esutlie/blender_creations/blender/stlexports/2021-10-08_16-44-18/stand.stl

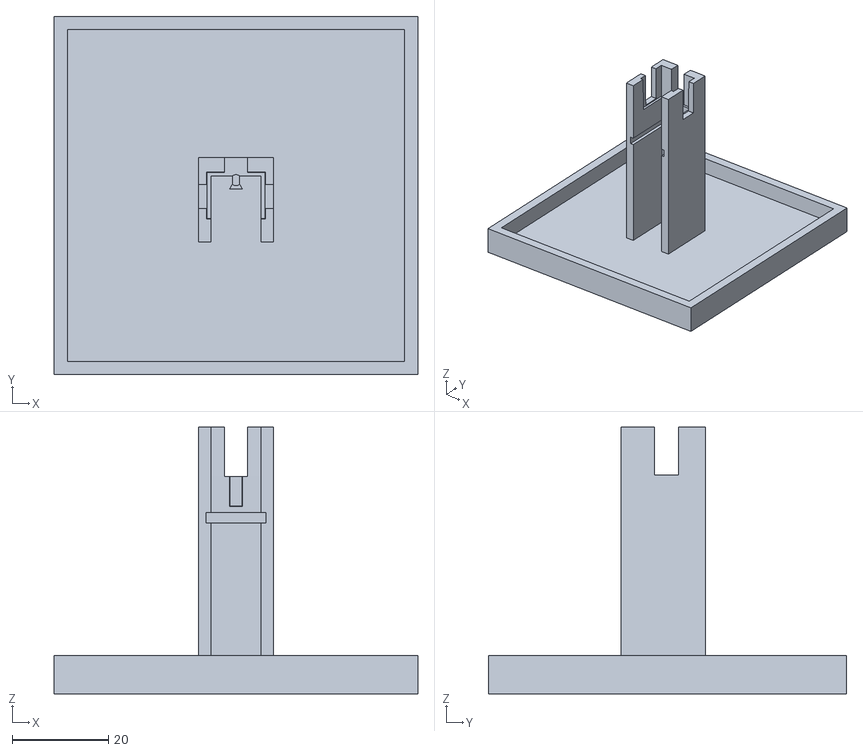
[picture p12: CAD file, 2021-10-22]
blender/stlexports/2021-10-08_16-44-18/stand.stl
75.7 x 74.6 x 55.5
