esutlie/blender_creations/blender/stlexports/2021-10-08_16-51-40/surgery.002.stl

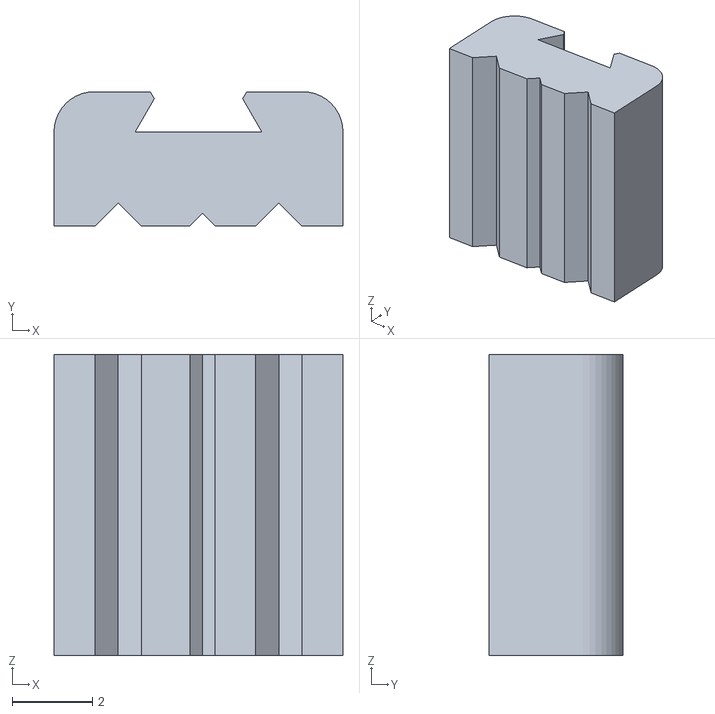
[picture p13: CAD file, 2021-10-22]
blender/stlexports/2021-10-08_16-51-40/surgery.002.stl
7.20 x 3.35 x 7.50
