esutlie/blender_creations/blender/stlexports/2021-10-11_14-52-31/cap0.2,0.13.stl

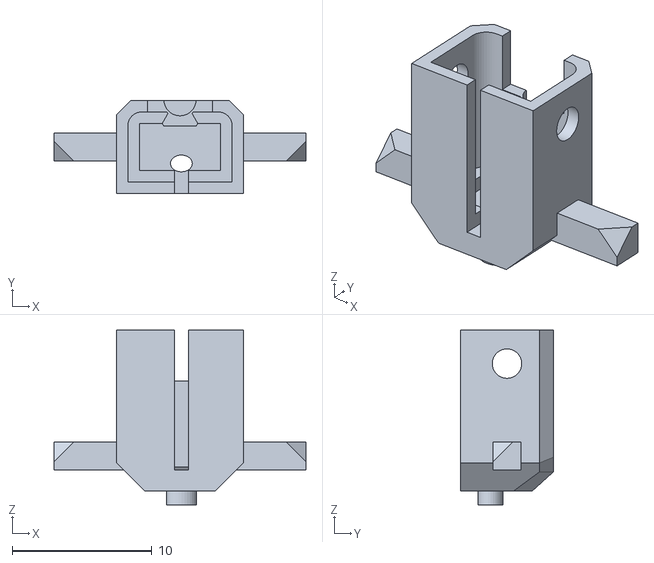
[picture p14: CAD file, 2021-10-22]
blender/stlexports/2021-10-11_14-52-31/cap0.2,0.13.stl
18.0 x 6.61 x 12.5
