esutlie/blender_creations/blender/stlexports/2021-10-11_14-56-39/surgery0.1.stl

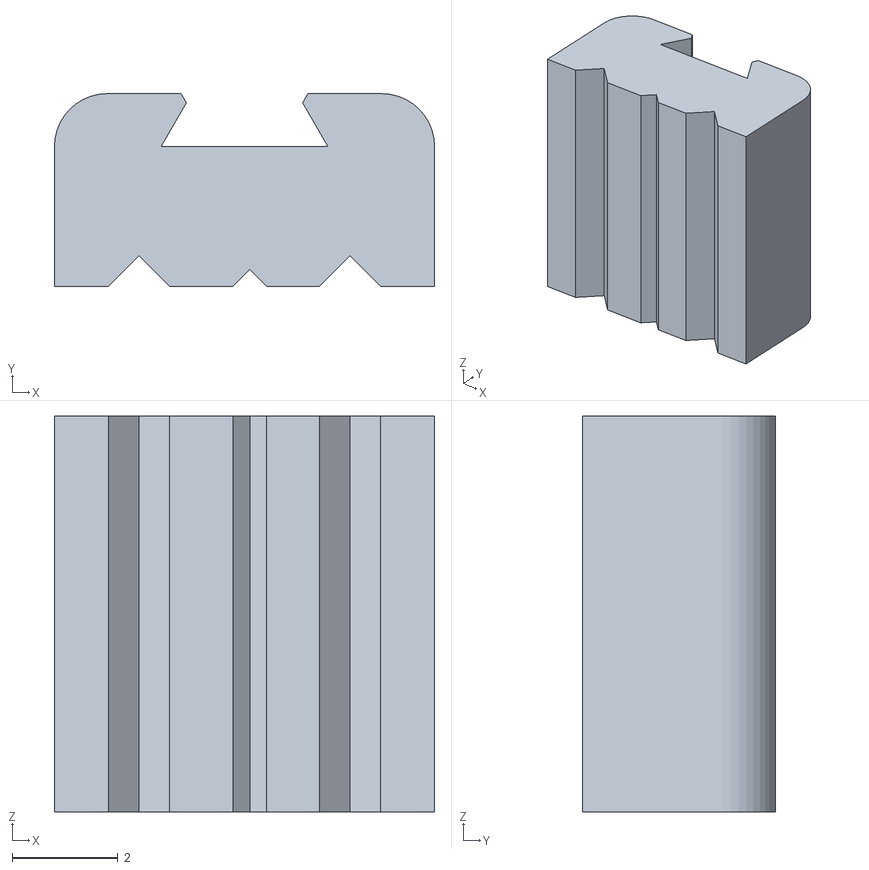
[picture p15: CAD file, 2021-10-22]
blender/stlexports/2021-10-11_14-56-39/surgery0.1.stl
7.20 x 3.65 x 7.50
