esutlie/blender_creations/blender/stlexports/2021-10-12_14-52-41/cover.stl

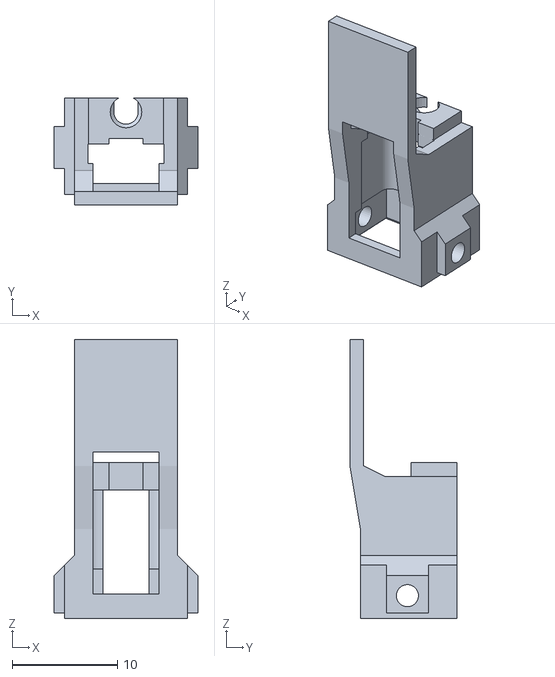
[picture p16: CAD file, 2021-10-22]
blender/stlexports/2021-10-12_14-52-41/cover.stl
13.6 x 10.2 x 26.5
