esutlie/blender_creations/blender/stlexports/2021-10-13_14-44-16/cover0.1.stl

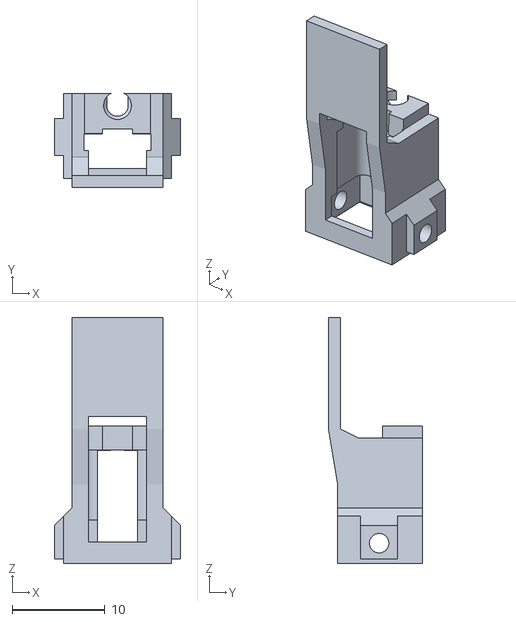
[picture p17: CAD file, 2021-10-22]
blender/stlexports/2021-10-13_14-44-16/cover0.1.stl
13.6 x 10.2 x 26.5
