esutlie/blender_creations/blender/stlexports/2021-10-22_11-58-40/cleaner.stl

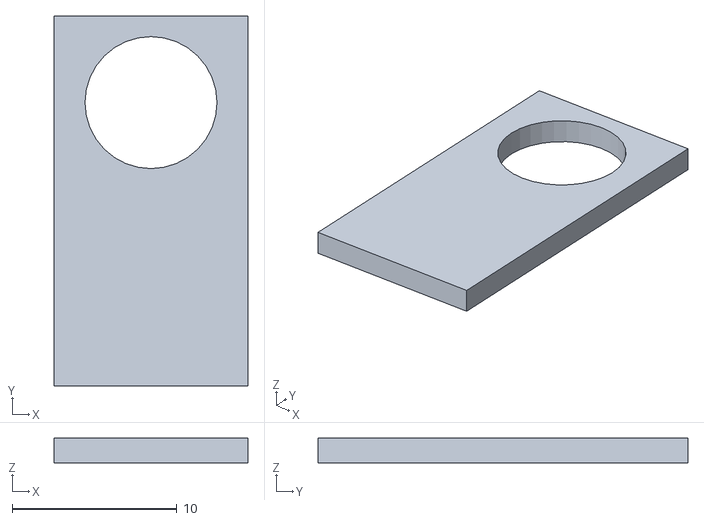
[picture p18: CAD file, 2021-10-29]
blender/stlexports/2021-10-22_11-58-40/cleaner.stl
11.8 x 22.4 x 1.50
