esutlie/blender_creations/blender/stlexports/2021-10-22_17-03-30/holder.stl

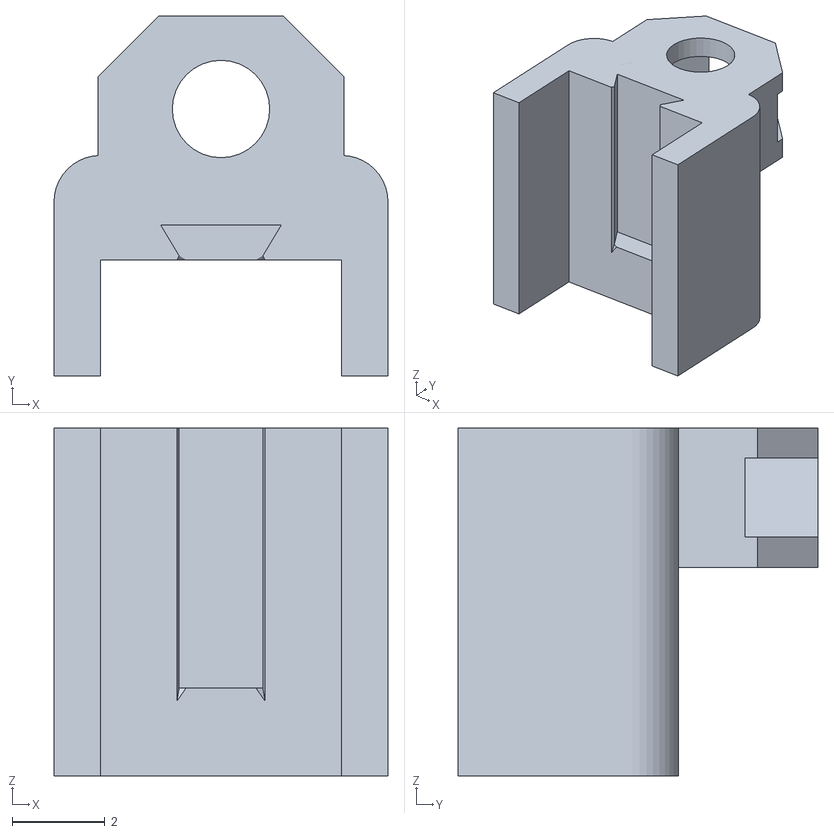
[picture p19: CAD file, 2021-10-29]
blender/stlexports/2021-10-22_17-03-30/holder.stl
7.20 x 7.75 x 7.50
