esutlie/blender_creations/blender/stlexports/2021-10-27_11-30-10/stand_test.stl

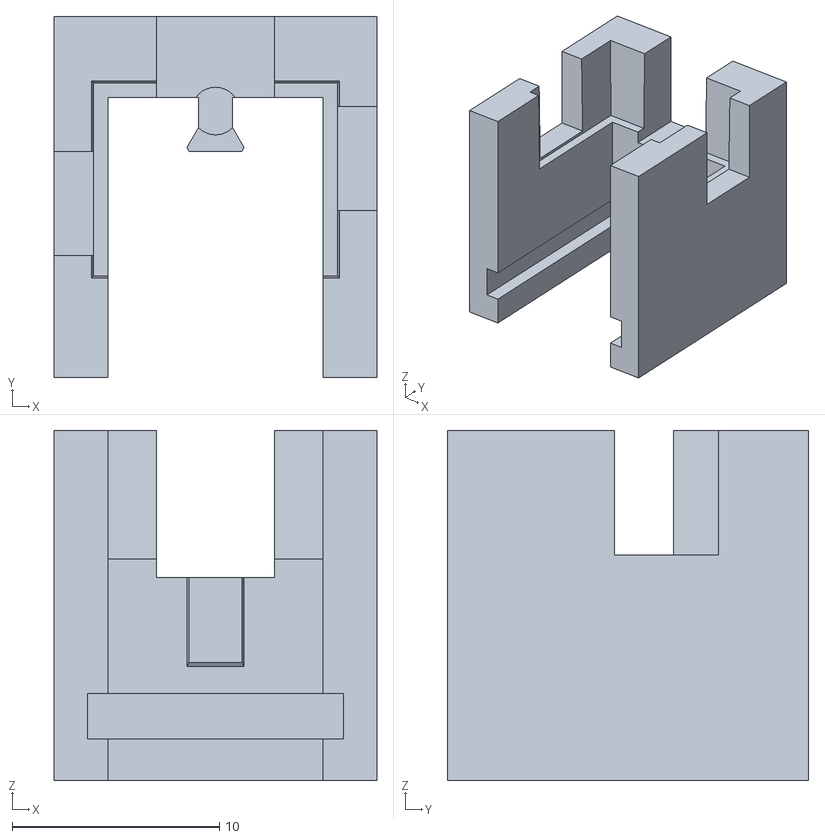
[picture p20: CAD file, 2021-10-29]
blender/stlexports/2021-10-27_11-30-10/stand_test.stl
15.6 x 17.4 x 16.9
