esutlie/blender_creations/blender/stlexports/2021-10-27_16-32-51/cap.stl

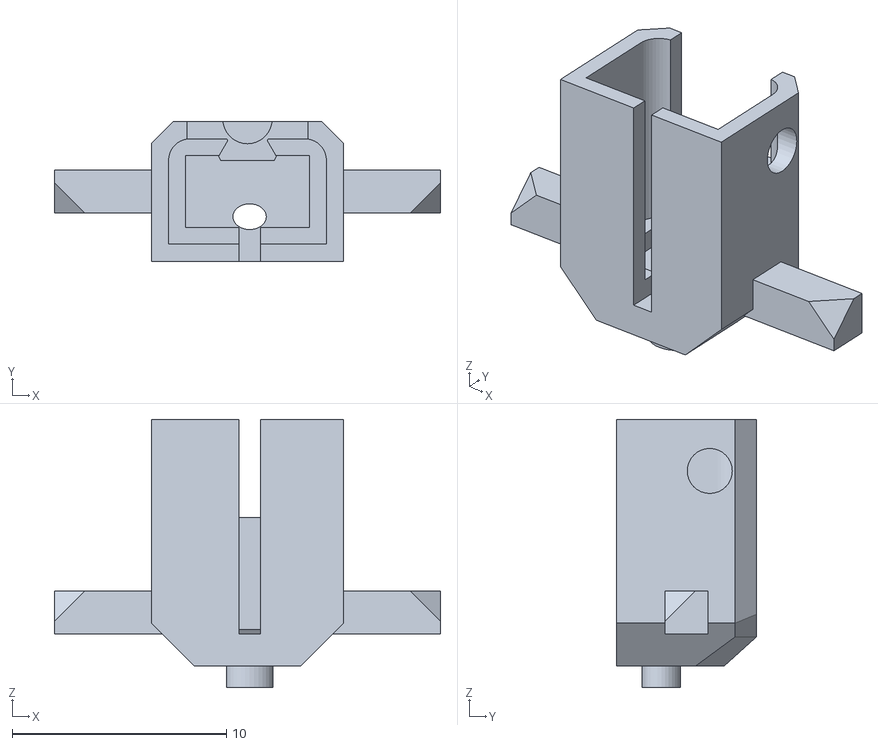
[picture p21: CAD file, 2021-10-29]
blender/stlexports/2021-10-27_16-32-51/cap.stl
18.0 x 6.51 x 12.5
