esutlie/blender_creations/blender/stlexports/2021-10-28_10-04-52/cover.stl

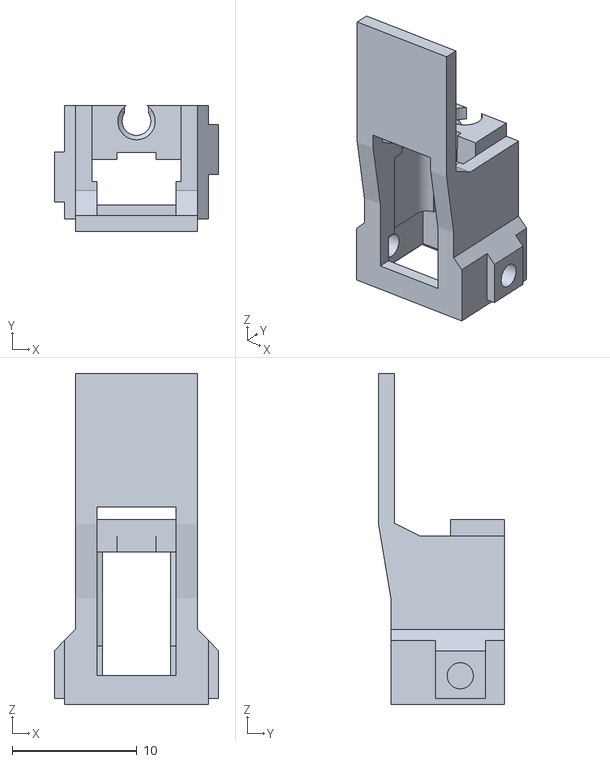
[picture p22: CAD file, 2021-10-29]
blender/stlexports/2021-10-28_10-04-52/cover.stl
13.2 x 10.1 x 26.5
