esutlie/blender_creations/blender/stlexports/2021-11-03_10-34-36/stand_test.stl

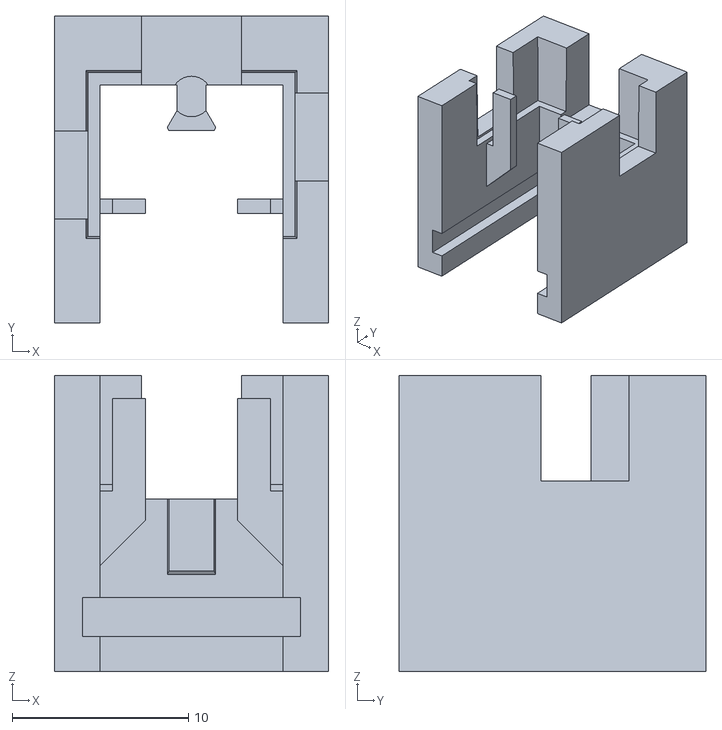
[picture p23: CAD file, 2022-01-04]
blender/stlexports/2021-11-03_10-34-36/stand_test.stl
15.6 x 17.4 x 16.8
