esutlie/blender_creations/blender/stlexports/2021-11-15_14-42-10/cam_cover.stl

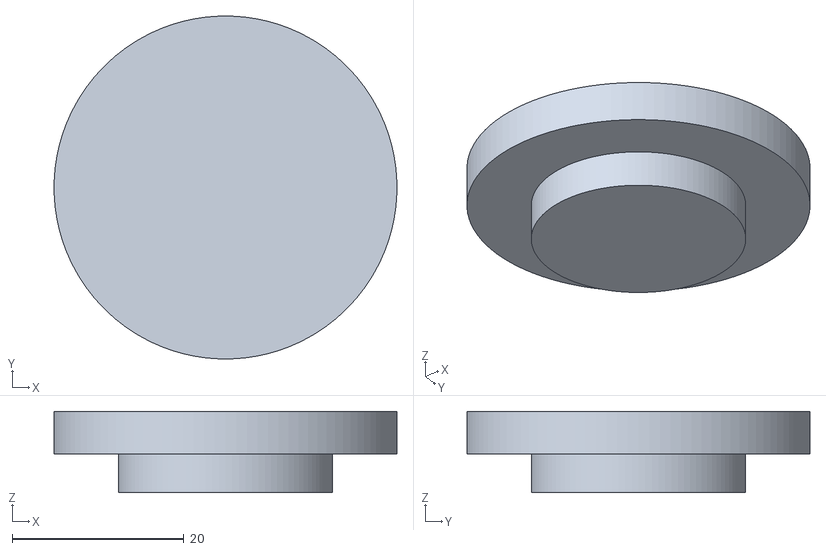
[picture p24: CAD file, 2022-01-04]
blender/stlexports/2021-11-15_14-42-10/cam_cover.stl
40.0 x 40.0 x 9.50
