esutlie/blender_creations/blender/stlexports/2021-11-15_14-51-04/stand.stl

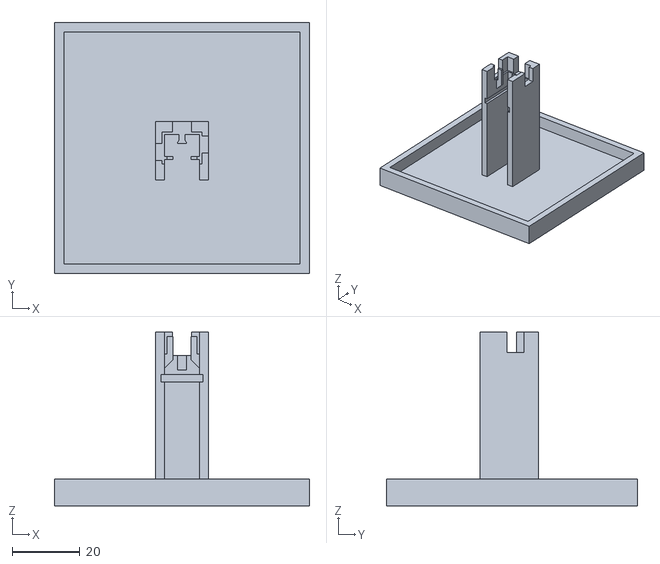
[picture p25: CAD file, 2022-01-04]
blender/stlexports/2021-11-15_14-51-04/stand.stl
75.6 x 74.4 x 51.5
