esutlie/blender_creations/blender/stlexports/2021-11-29_10-13-55/cam_attach.stl

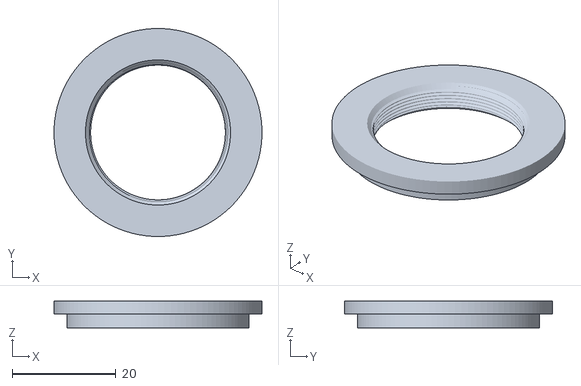
[picture p26: CAD file, 2022-01-04]
blender/stlexports/2021-11-29_10-13-55/cam_attach.stl
40.0 x 40.0 x 5.10
