esutlie/blender_creations/blender/stlexports/2021-12-08_10-14-58/holder.stl

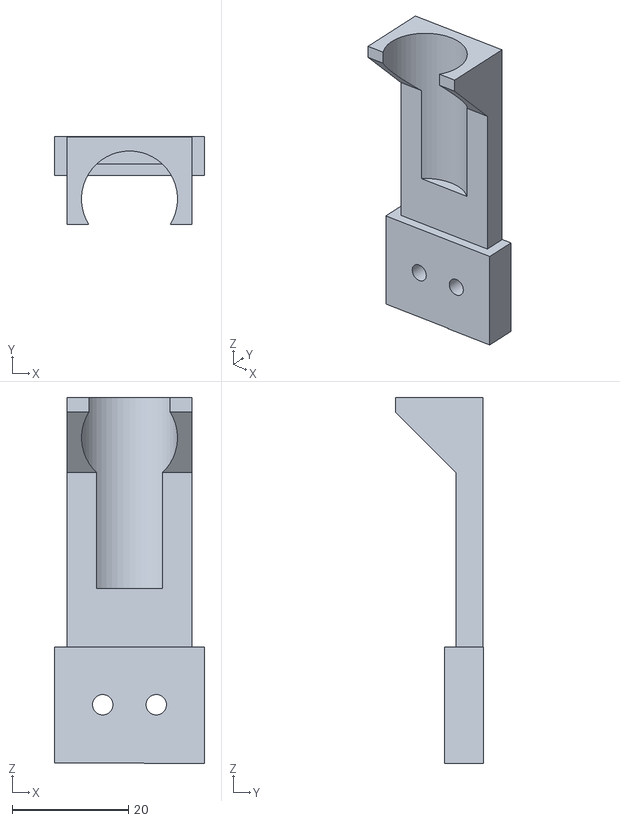
[picture p27: CAD file, 2022-01-04]
blender/stlexports/2021-12-08_10-14-58/holder.stl
25.8 x 15.1 x 62.9
