esutlie/blender_creations/blender/stlexports/2021-12-08_15-39-04/holder.stl

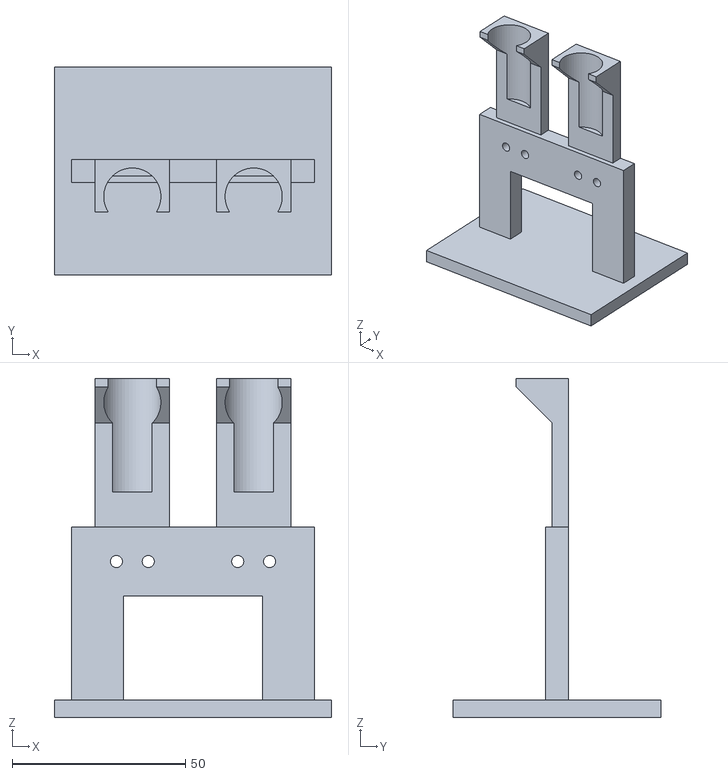
[picture p28: CAD file, 2022-01-04]
blender/stlexports/2021-12-08_15-39-04/holder.stl
80.0 x 60.0 x 97.8
