esutlie/blender_creations/blender/stlexports/2021-12-09_09-44-28/holder.stl

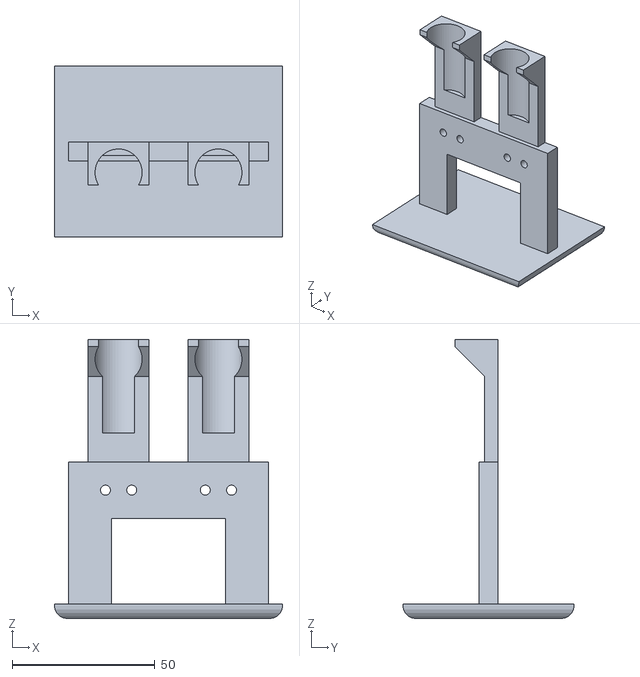
[picture p29: CAD file, 2022-01-04]
blender/stlexports/2021-12-09_09-44-28/holder.stl
80.0 x 60.0 x 97.8
