esutlie/blender_creations/blender/stlexports/2021-12-09_09-47-33/holder.stl

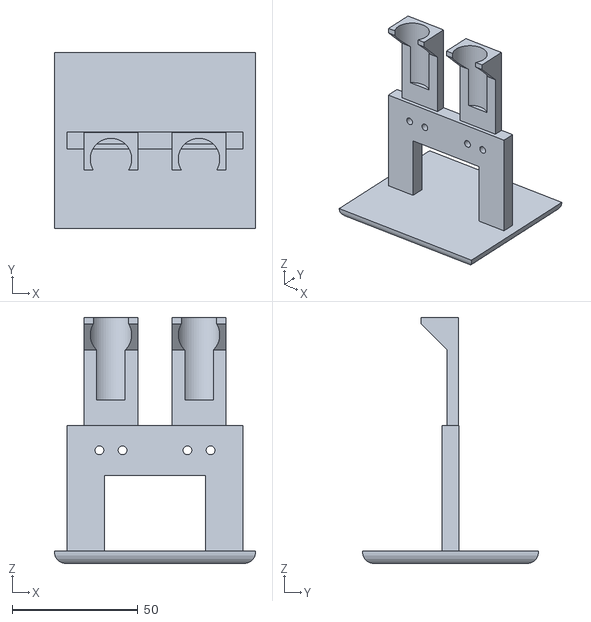
[picture p30: CAD file, 2022-01-04]
blender/stlexports/2021-12-09_09-47-33/holder.stl
80.0 x 70.0 x 97.8
