esutlie/blender_creations/blender/stlexports/2021-12-14_14-30-24/tri.stl

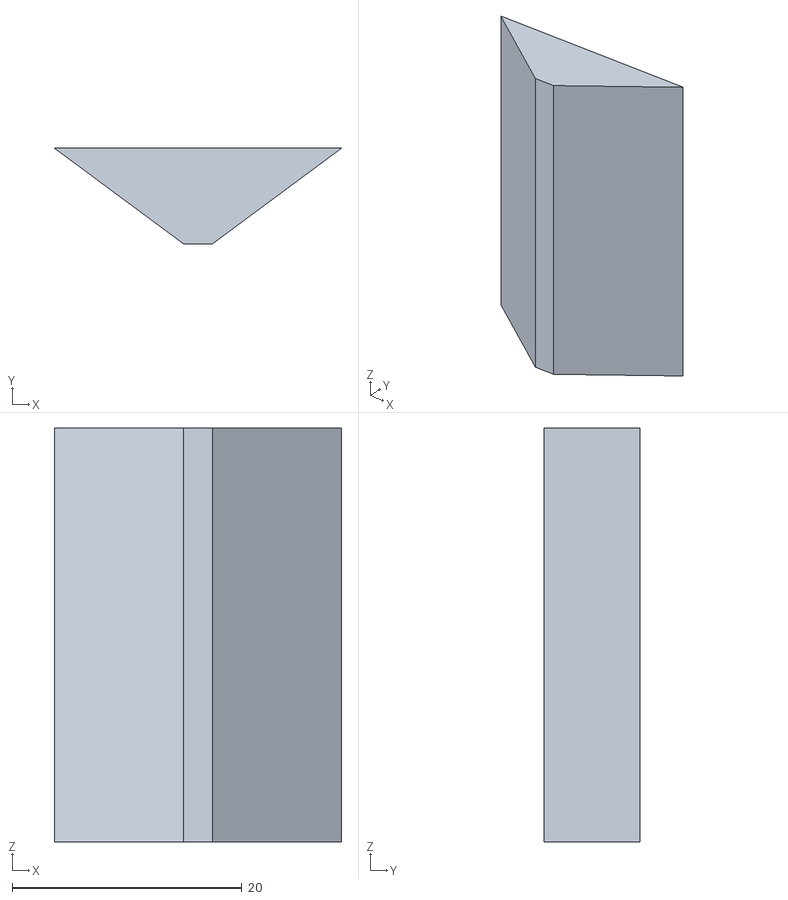
[picture p31: CAD file, 2022-01-04]
blender/stlexports/2021-12-14_14-30-24/tri.stl
25.0 x 8.33 x 36.0
