esutlie/blender_creations/blender/stlexports/2021-12-14_15-07-16/tri.stl

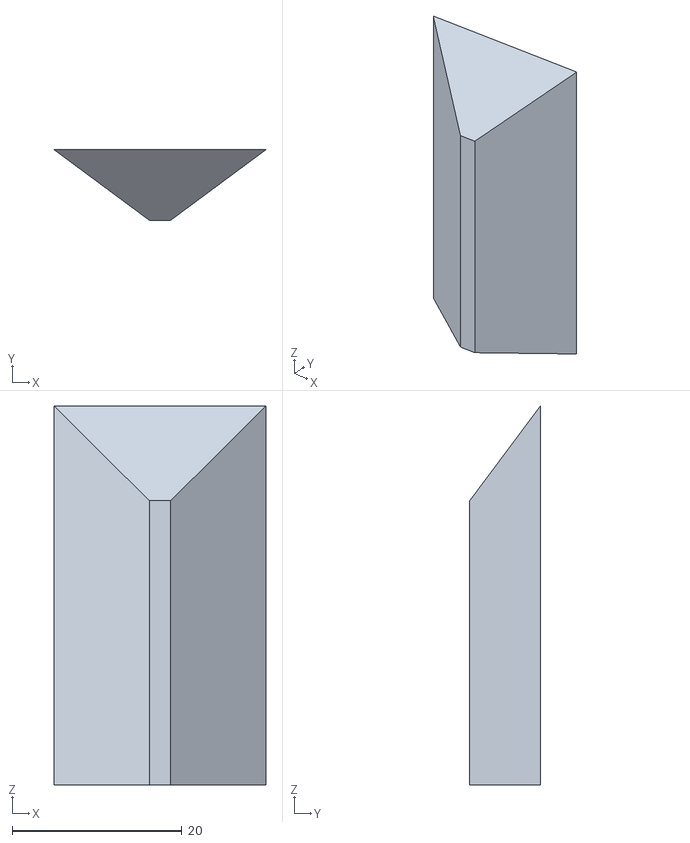
[picture p32: CAD file, 2022-01-04]
blender/stlexports/2021-12-14_15-07-16/tri.stl
25.0 x 8.33 x 44.7
