esutlie/blender_creations/blender/stlexports/2021-12-15_12-07-13/backer.stl

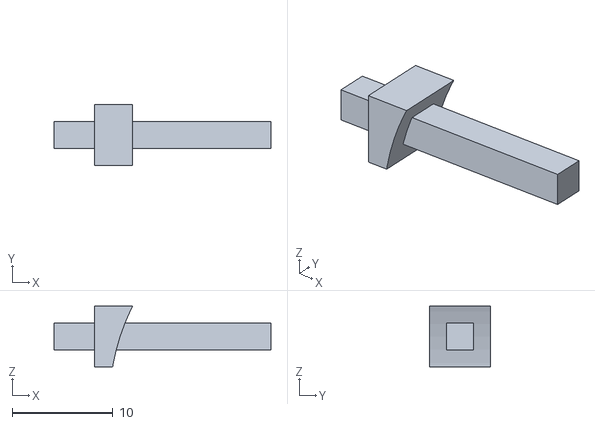
[picture p33: CAD file, 2022-01-04]
blender/stlexports/2021-12-15_12-07-13/backer.stl
21.5 x 6.00 x 6.00
