esutlie/blender_creations/blender/stlexports/2022-01-04_11-12-24/tube.stl

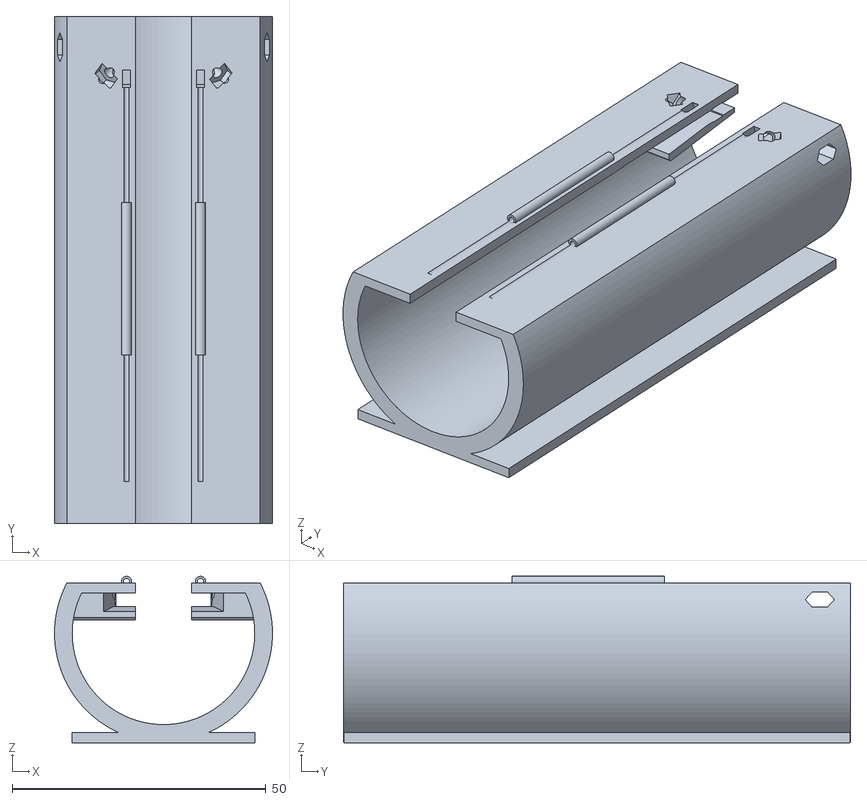
[picture p34: CAD file, 2022-01-04]
blender/stlexports/2022-01-04_11-12-24/tube.stl
43.0 x 100.0 x 32.9
