esutlie/blender_creations/blender/stlexports/2022-01-05_09-46-58/holder.stl

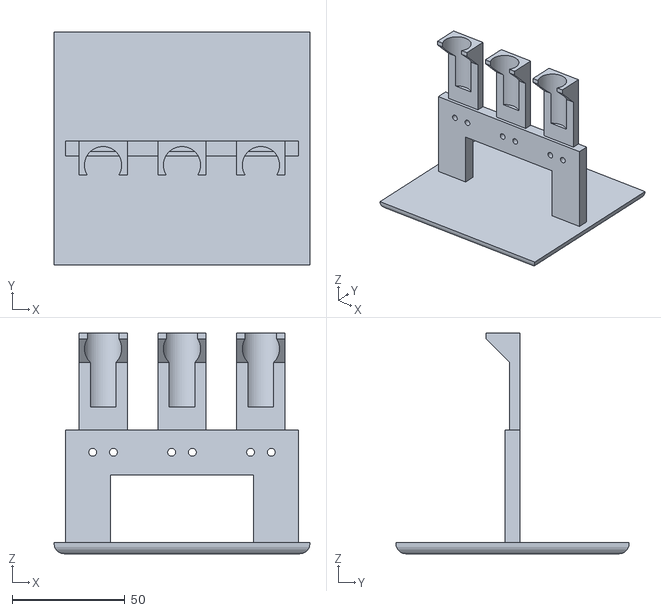
[picture p35: CAD file, 2022-01-31]
blender/stlexports/2022-01-05_09-46-58/holder.stl
113.5 x 103.5 x 97.8
