esutlie/blender_creations/blender/stlexports/2022-01-05_09-47-00/creation.stl

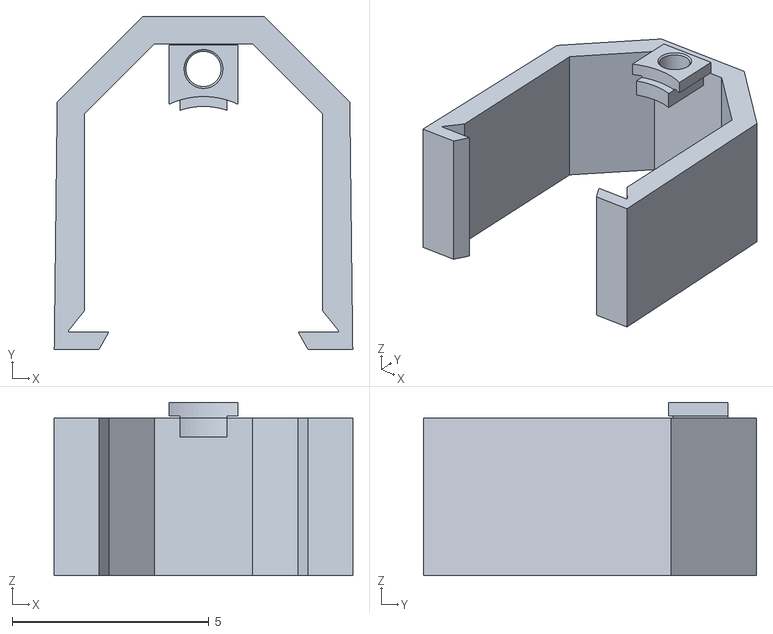
[picture p36: CAD file, 2022-01-31]
blender/stlexports/2022-01-05_09-47-00/creation.stl
7.58 x 8.46 x 4.40
