esutlie/blender_creations/blender/stlexports/2022-01-28_13-01-05/cable_cover.stl

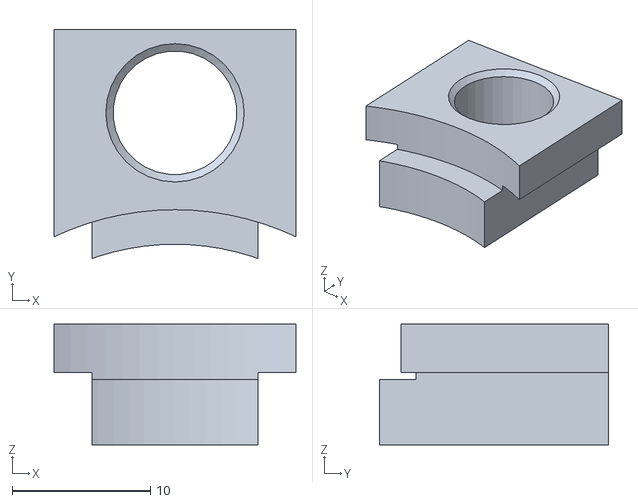
[picture p37: CAD file, 2022-01-31]
blender/stlexports/2022-01-28_13-01-05/cable_cover.stl
17.5 x 16.6 x 8.75
