esutlie/blender_creations/blender/stlexports/2022-02-18_14-35-42/cleaner.stl

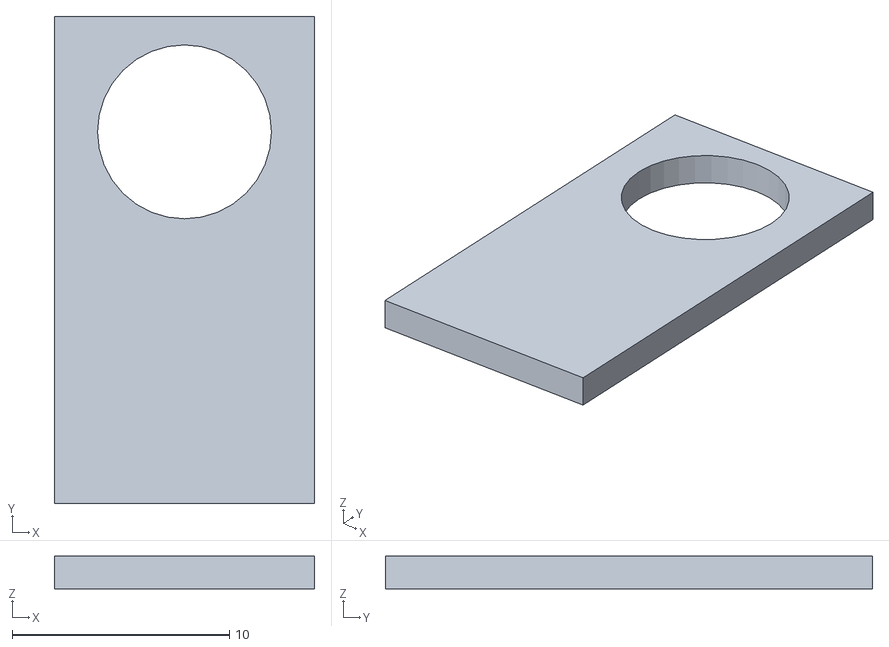
[picture p38: CAD file, 2022-02-21]
blender/stlexports/2022-02-18_14-35-42/cleaner.stl
12.0 x 22.4 x 1.50
