esutlie/blender_creations/blender/stlexports/2022-02-25_14-08-06/cover.stl

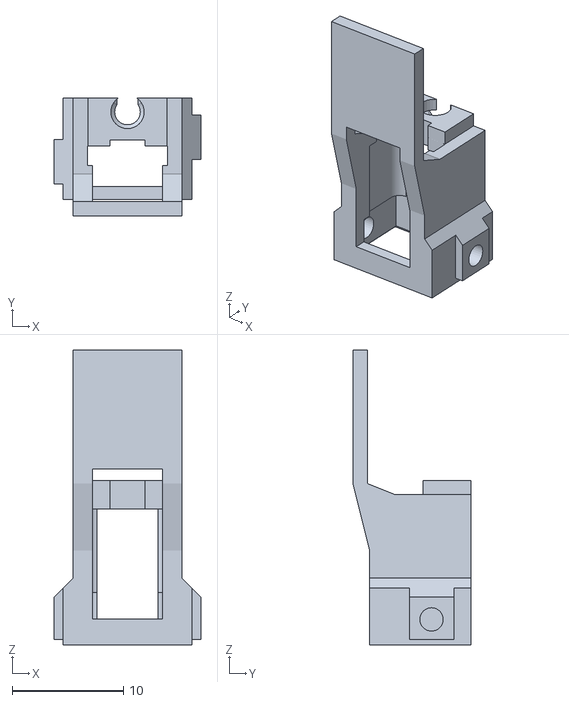
[picture p39: CAD file, 2022-09-09]
blender/stlexports/2022-02-25_14-08-06/cover.stl
13.2 x 10.6 x 26.5
