esutlie/blender_creations/blender/stlexports/2022-03-31_11-08-54/port.stl

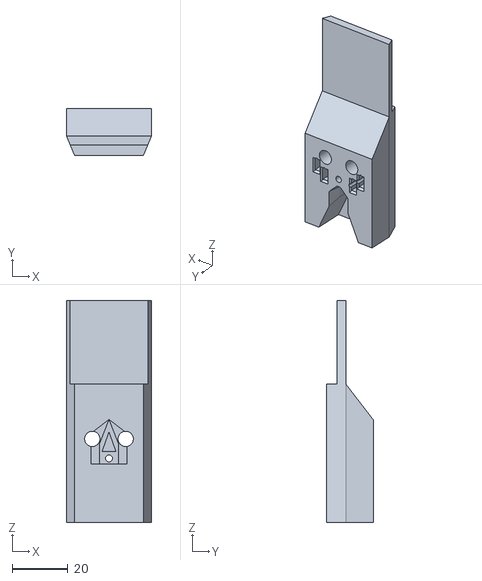
[picture p40: CAD file, 2022-09-09]
blender/stlexports/2022-03-31_11-08-54/port.stl
30.5 x 17.0 x 79.7
