esutlie/blender_creations/blender/stlexports/2022-04-05_10-54-50/port.stl

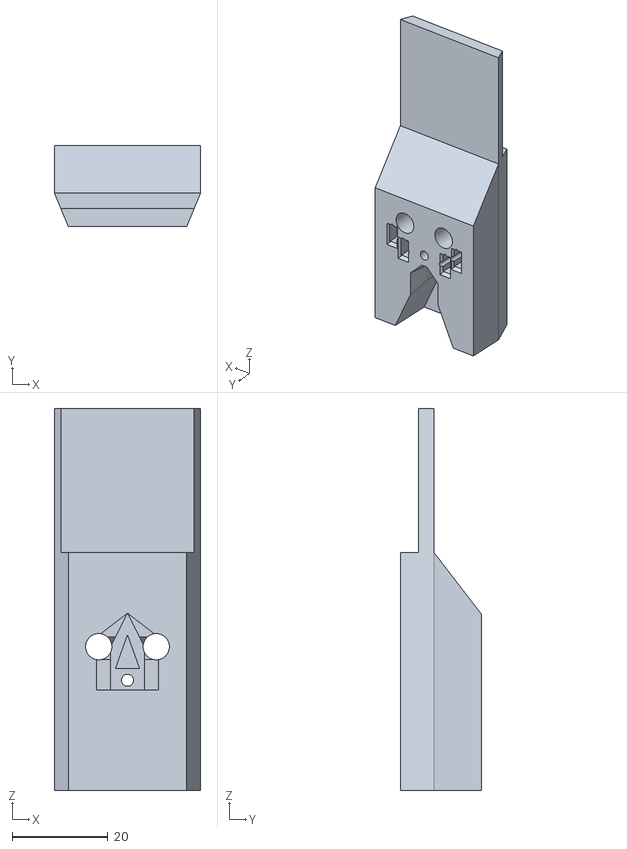
[picture p41: CAD file, 2022-09-09]
blender/stlexports/2022-04-05_10-54-50/port.stl
30.5 x 17.0 x 79.7
