esutlie/blender_creations/blender/stlexports/2022-05-19_14-07-43_tictac/frame.stl

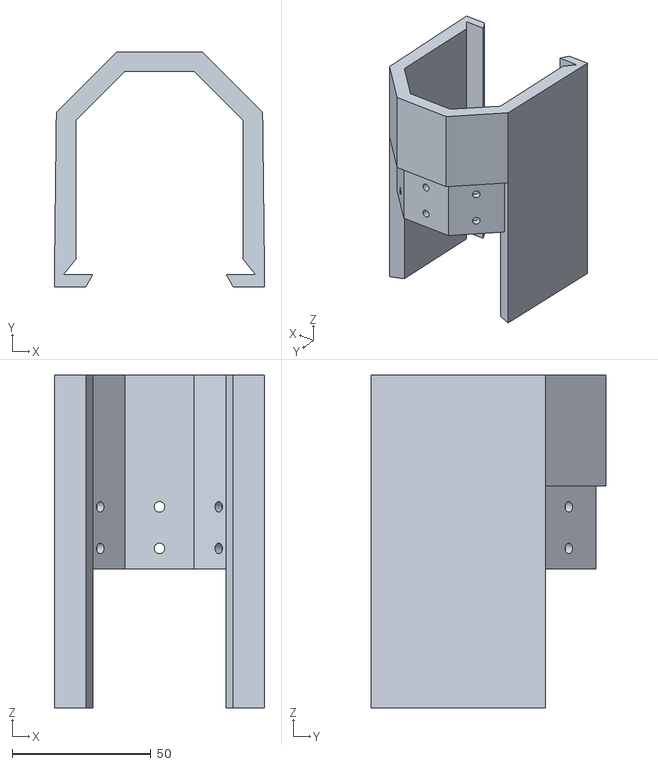
[picture p42: CAD file, 2022-09-09]
blender/stlexports/2022-05-19_14-07-43_tictac/frame.stl
75.8 x 84.6 x 120.0
