esutlie/blender_creations/blender/stlexports/2022-08-19_12-06-19/cap0.02.stl

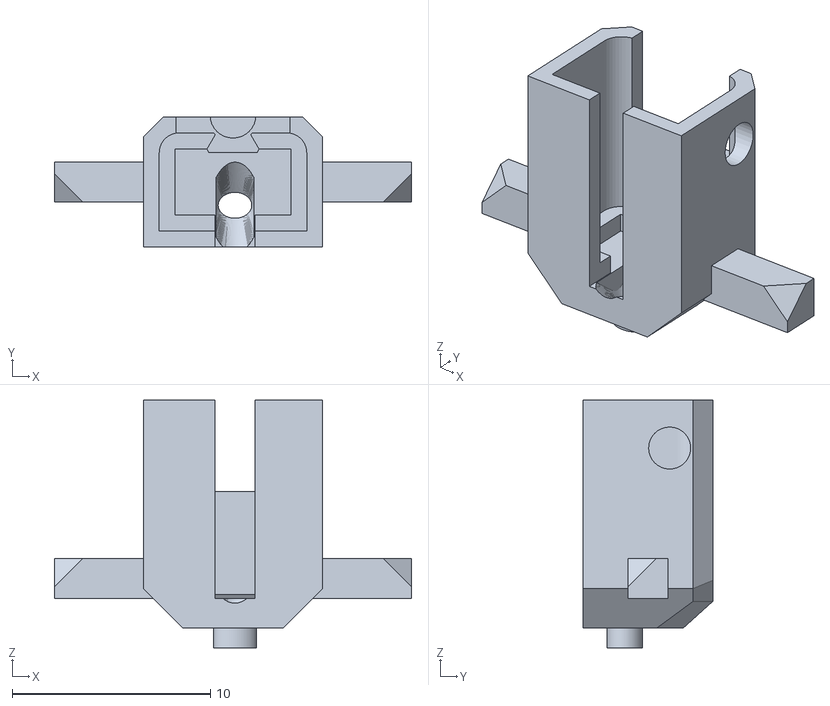
[picture p43: CAD file, 2022-09-09]
blender/stlexports/2022-08-19_12-06-19/cap0.02.stl
18.0 x 6.55 x 12.5
