esutlie/blender_creations/blender/stlexports/2022-08-19_12-06-27/cover0.04.stl

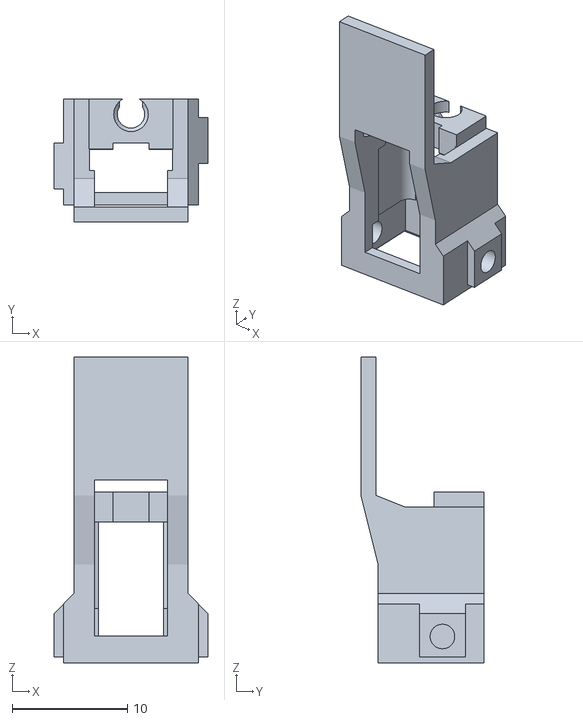
[picture p44: CAD file, 2022-09-09]
blender/stlexports/2022-08-19_12-06-27/cover0.04.stl
13.3 x 10.7 x 26.5
