esutlie/blender_creations/blender/stlexports/2022-08-19_12-06-36/surgery0.06.stl

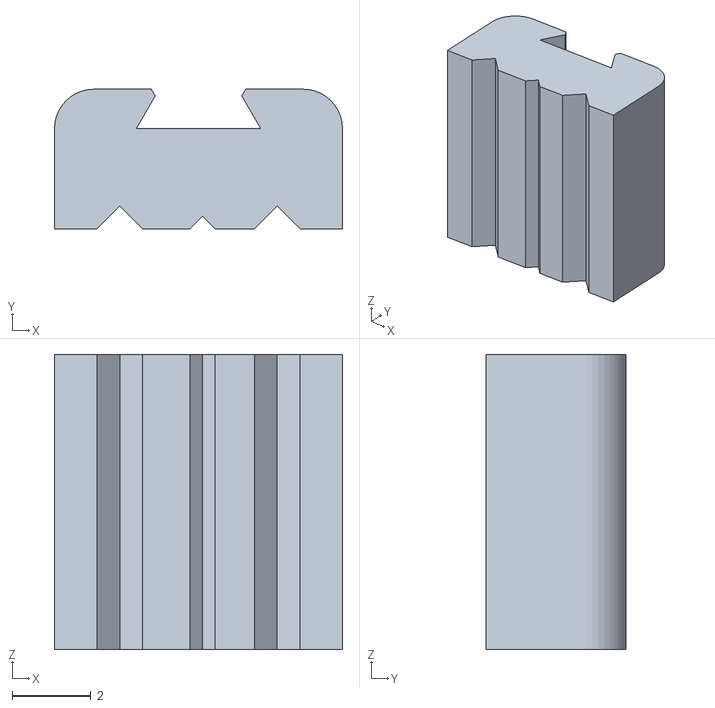
[picture p45: CAD file, 2022-09-09]
blender/stlexports/2022-08-19_12-06-36/surgery0.06.stl
7.32 x 3.55 x 7.50
