esutlie/blender_creations/blender/stlexports/2022-08-19_12-06-45/cap0.08.stl

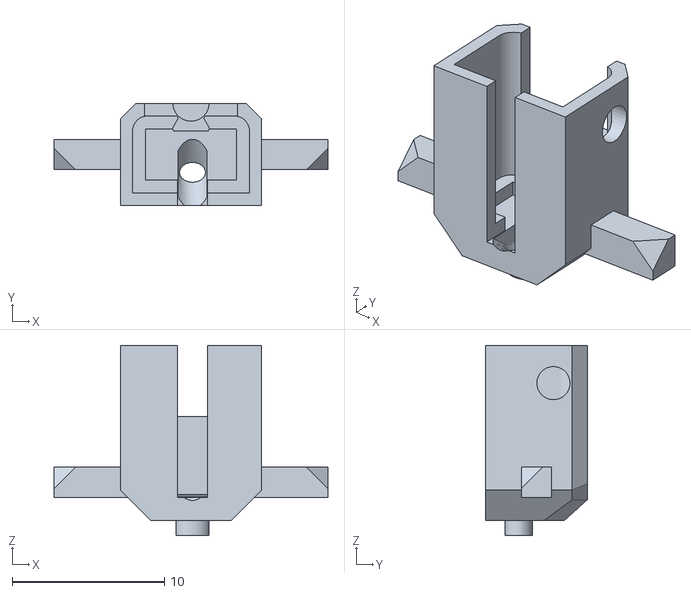
[picture p46: CAD file, 2022-09-09]
blender/stlexports/2022-08-19_12-06-45/cap0.08.stl
18.0 x 6.67 x 12.5
