esutlie/blender_creations/blender/stlexports/2022-08-19_12-06-52/holder0.1.stl

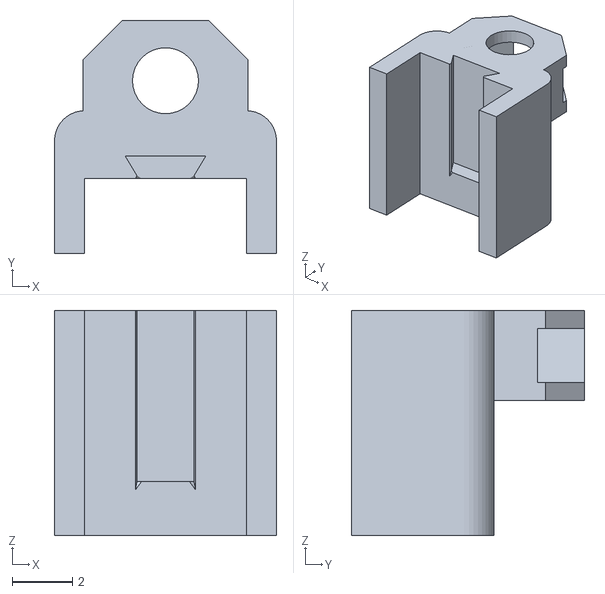
[picture p47: CAD file, 2022-09-09]
blender/stlexports/2022-08-19_12-06-52/holder0.1.stl
7.40 x 7.75 x 7.50
