esutlie/blender_creations/blender/stlexports/2022-08-22_11-59-44/cap-0.06.stl

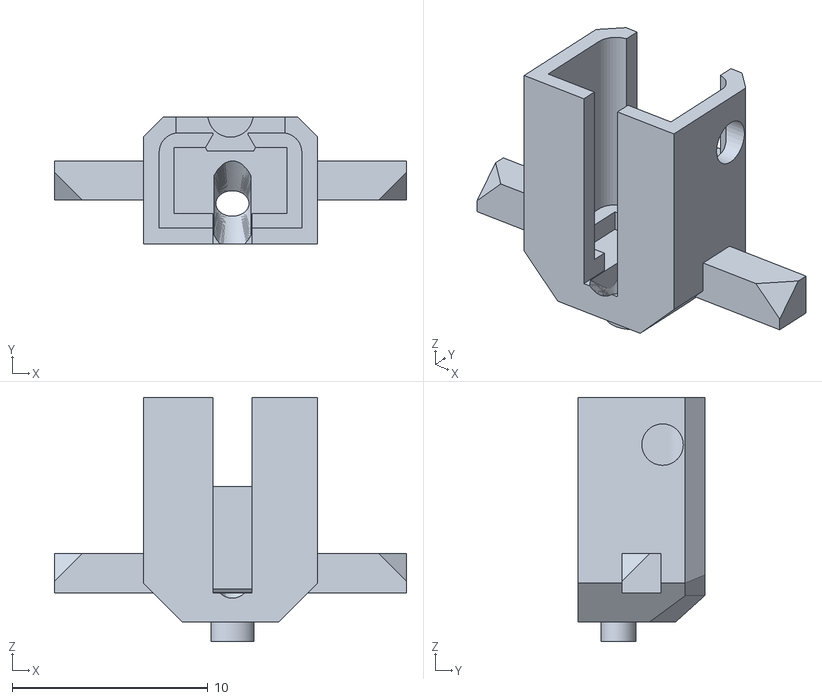
[picture p48: CAD file, 2022-09-09]
blender/stlexports/2022-08-22_11-59-44/cap-0.06.stl
18.0 x 6.47 x 12.5
