esutlie/blender_creations/blender/stlexports/2022-08-22_11-59-57/stopper0.06.stl

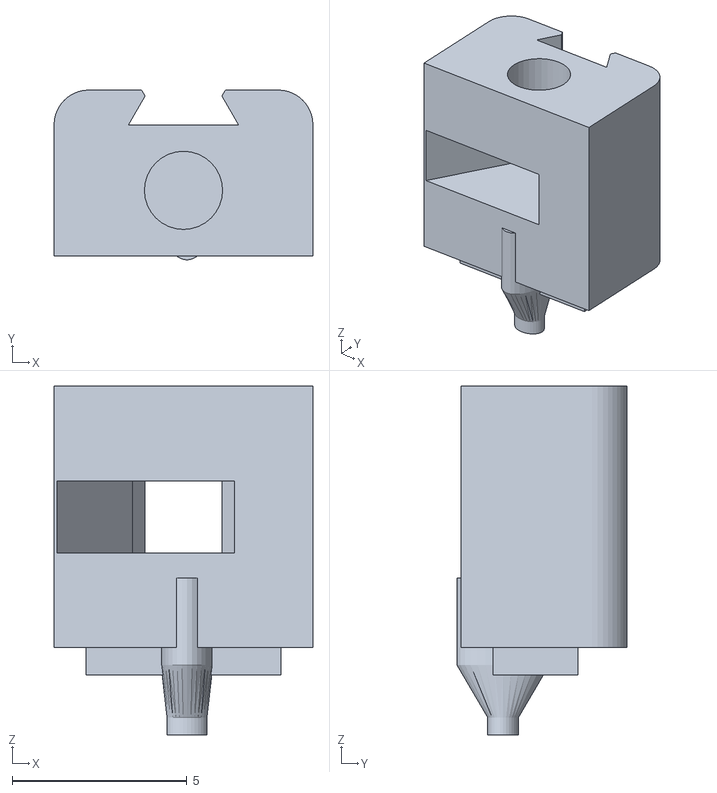
[picture p49: CAD file, 2022-09-09]
blender/stlexports/2022-08-22_11-59-57/stopper0.06.stl
7.42 x 4.87 x 10.0
