esutlie/blender_creations/blender/stlexports/2022-08-22_17-14-23/holder0.001.stl

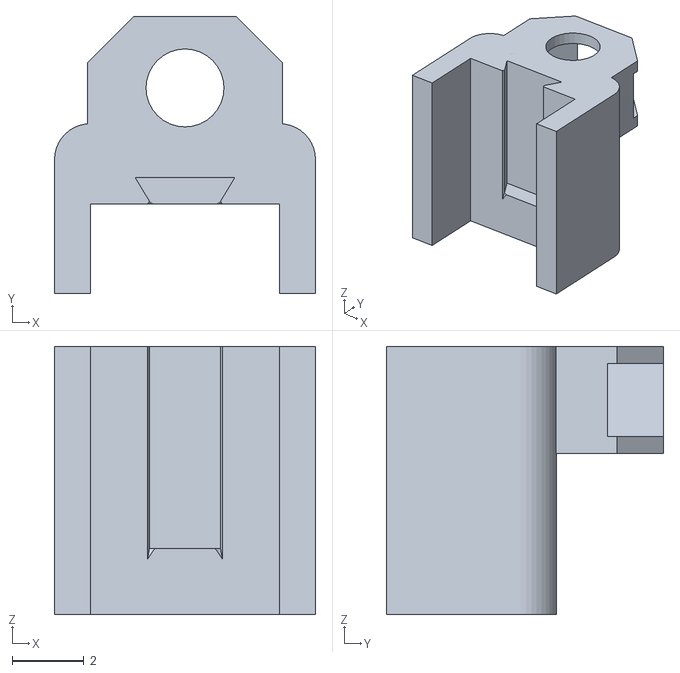
[picture p50: CAD file, 2022-09-09]
blender/stlexports/2022-08-22_17-14-23/holder0.001.stl
7.30 x 7.75 x 7.50
