esutlie/blender_creations/blender/stlexports/2022-08-22_17-14-26/cap0.stl

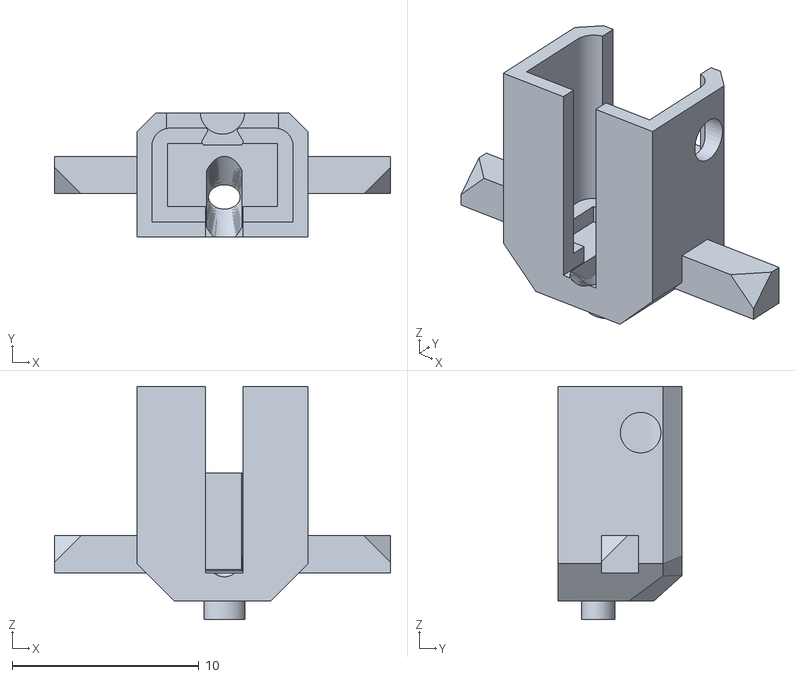
[picture p51: CAD file, 2022-09-09]
blender/stlexports/2022-08-22_17-14-26/cap0.stl
18.0 x 6.63 x 12.5
