esutlie/blender_creations/blender/stlexports/2022-08-23_11-19-07/stand.stl

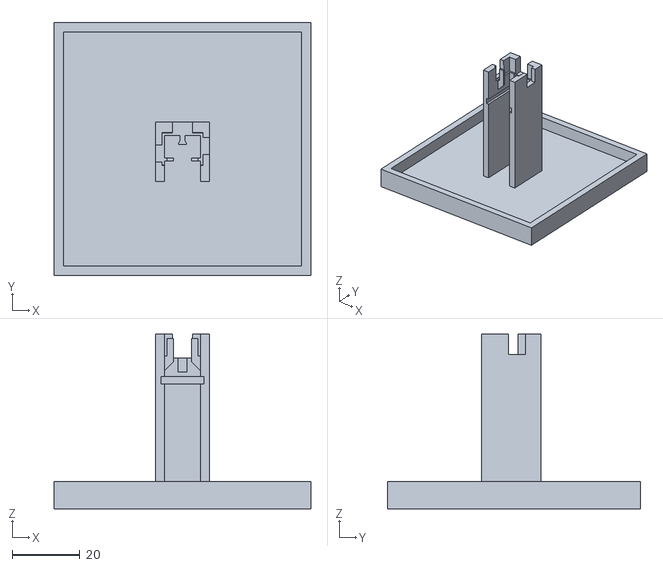
[picture p52: CAD file, 2022-09-09]
blender/stlexports/2022-08-23_11-19-07/stand.stl
75.8 x 74.6 x 51.5
