esutlie/blender_creations/blender/stlexports/2022-08-23_16-00-06/cap0.stl

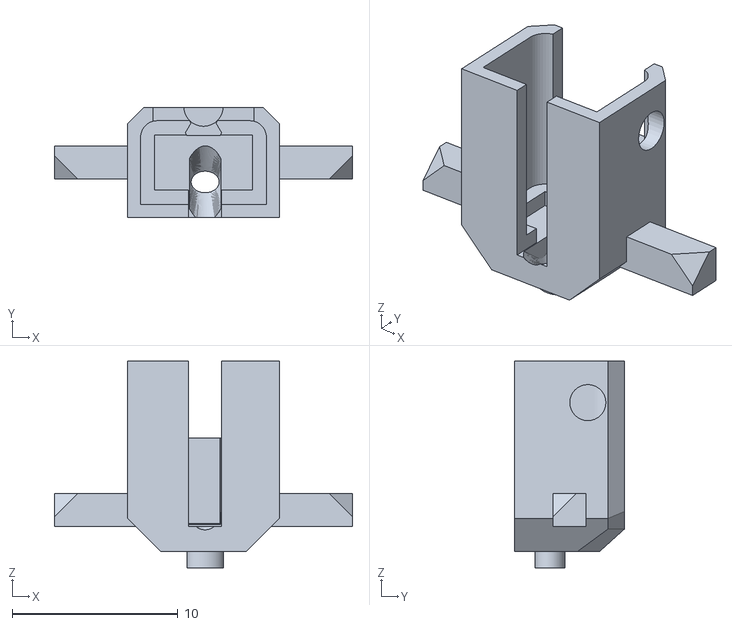
[picture p53: CAD file, 2022-09-09]
blender/stlexports/2022-08-23_16-00-06/cap0.stl
18.0 x 6.65 x 12.5
