esutlie/blender_creations/blender/stlexports/2022-08-30_17-17-07/holder0.6.stl

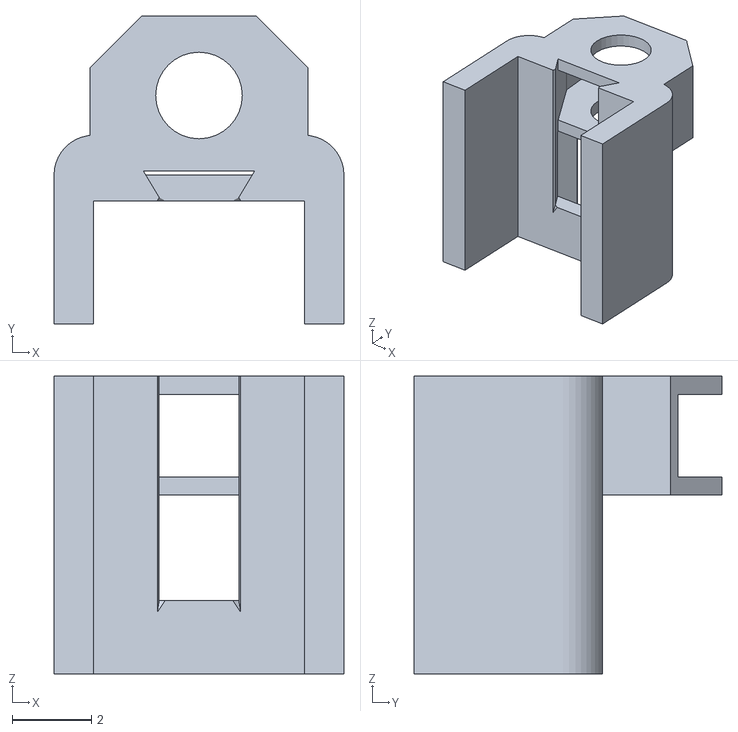
[picture p55: CAD file, 2022-09-09]
blender/stlexports/2022-08-30_17-17-07/holder0.6.stl
7.30 x 7.75 x 7.50
