esutlie/blender_creations/blender/stlexports/2021-09-28_10-52-53/holder.stl

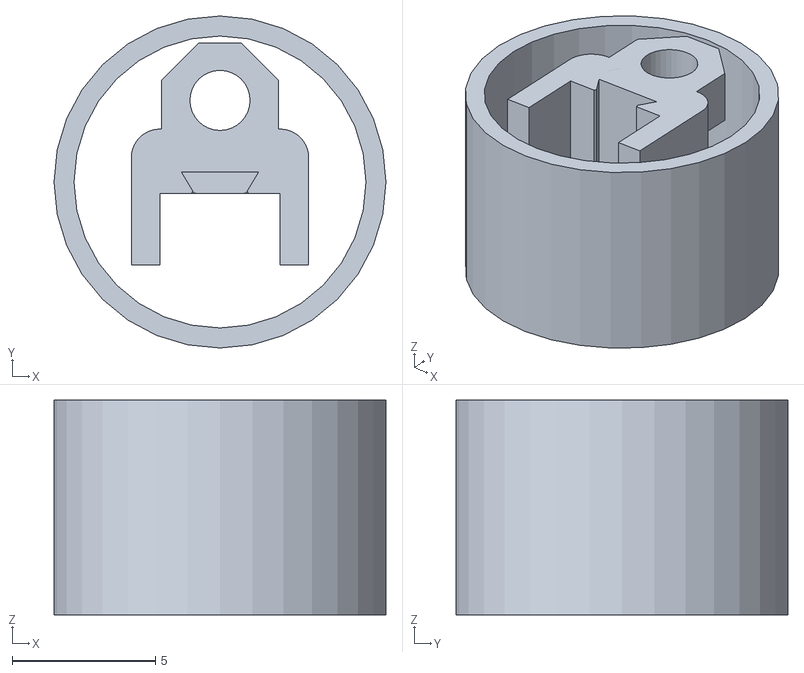
[picture p56: CAD file, 2021-10-06]
blender/stlexports/2021-09-28_10-52-53/holder.stl
11.6 x 11.6 x 7.50
