esutlie/blender_creations/blender/stlexports/2021-09-29_13-45-59/cap.stl

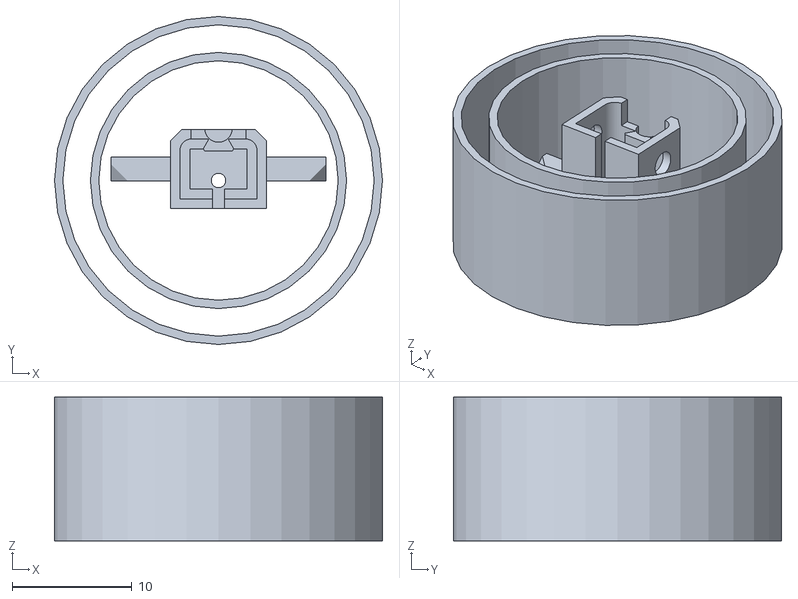
[picture p57: CAD file, 2021-10-06]
blender/stlexports/2021-09-29_13-45-59/cap.stl
27.4 x 27.4 x 12.0
