esutlie/blender_creations/blender/stlexports/2021-10-07_14-18-41/stopper.stl

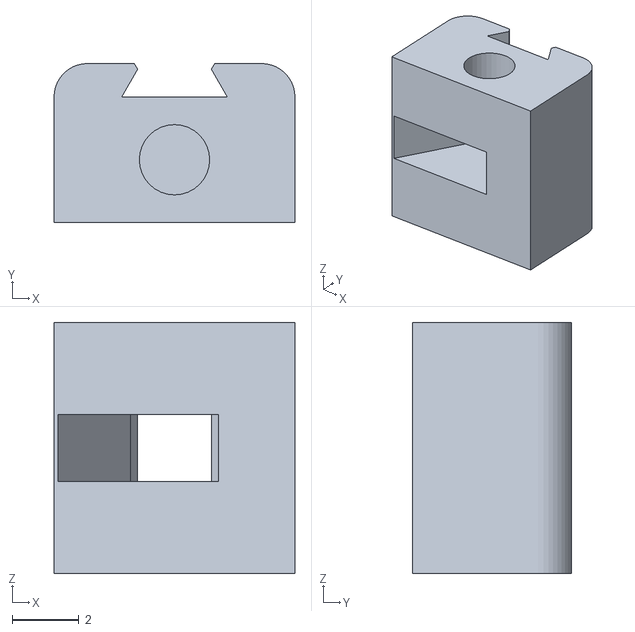
[picture p58: CAD file, 2021-10-22]
blender/stlexports/2021-10-07_14-18-41/stopper.stl
7.20 x 4.75 x 7.50
