esutlie/blender_creations/blender/stlexports/2021-10-08_16-44-18/cap0.15.stl

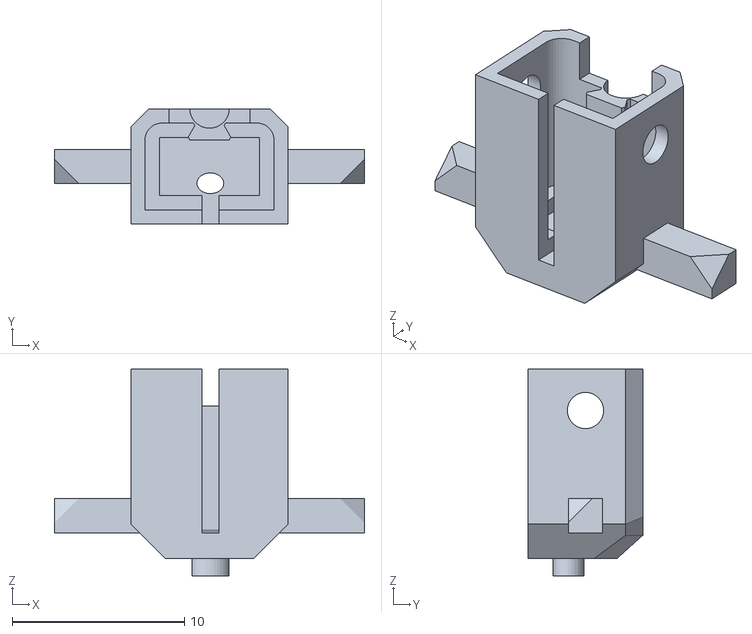
[picture p59: CAD file, 2021-10-22]
blender/stlexports/2021-10-08_16-44-18/cap0.15.stl
18.0 x 6.65 x 12.0
