esutlie/blender_creations/blender/stlexports/2021-10-11_14-56-39/surgery0.stl

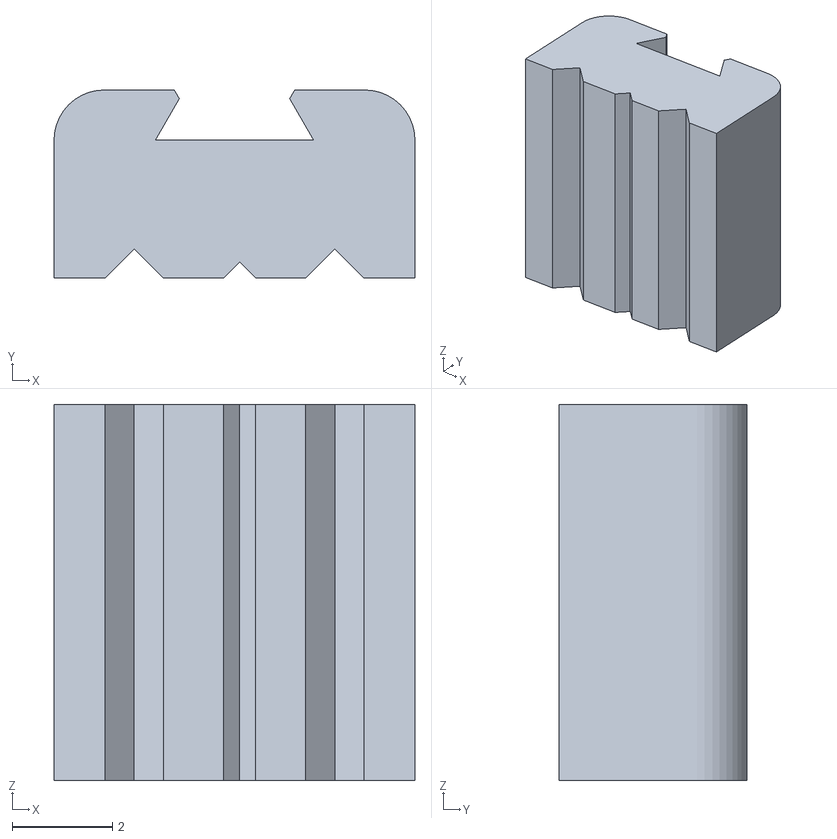
[picture p60: CAD file, 2021-10-22]
blender/stlexports/2021-10-11_14-56-39/surgery0.stl
7.20 x 3.75 x 7.50
