esutlie/blender_creations/blender/stlexports/2021-11-15_14-42-10/port.stl

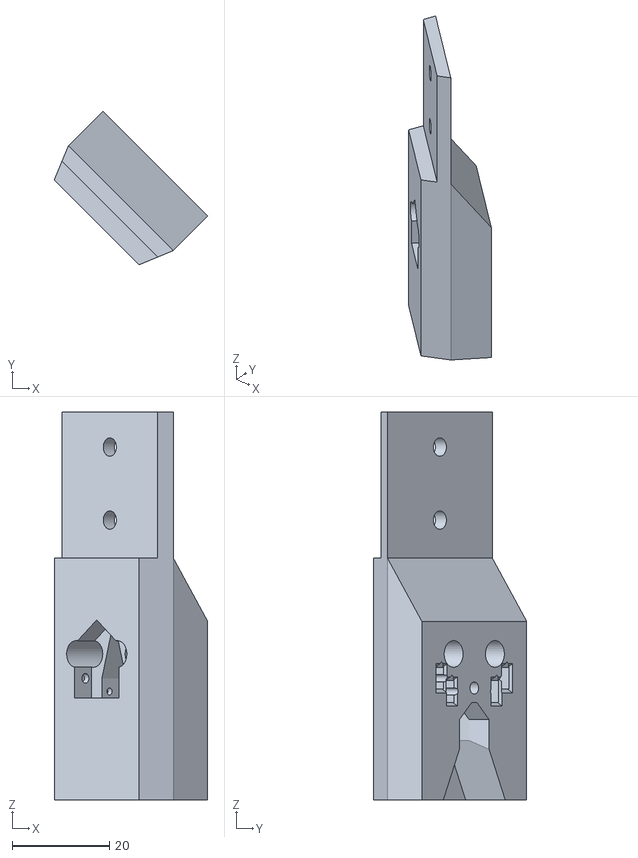
[picture p61: CAD file, 2022-01-04]
blender/stlexports/2021-11-15_14-42-10/port.stl
31.5 x 31.5 x 79.7
