esutlie/blender_creations/blender/stlexports/2021-11-29_13-33-59/cable_cover.stl

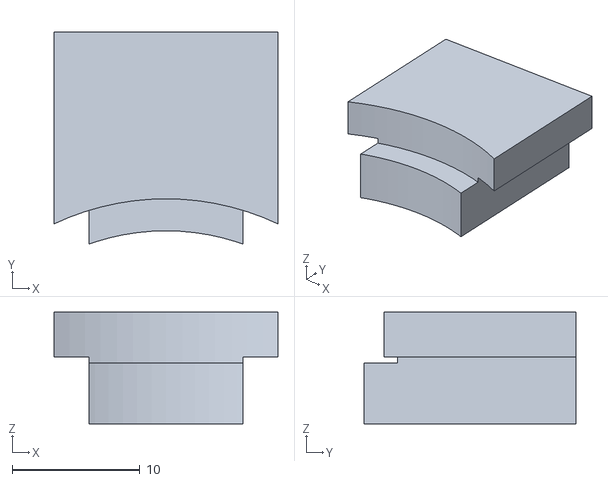
[picture p62: CAD file, 2022-01-04]
blender/stlexports/2021-11-29_13-33-59/cable_cover.stl
17.5 x 16.6 x 8.75
