esutlie/blender_creations/blender/stlexports/2022-08-19_12-06-45/stopper0.08.stl

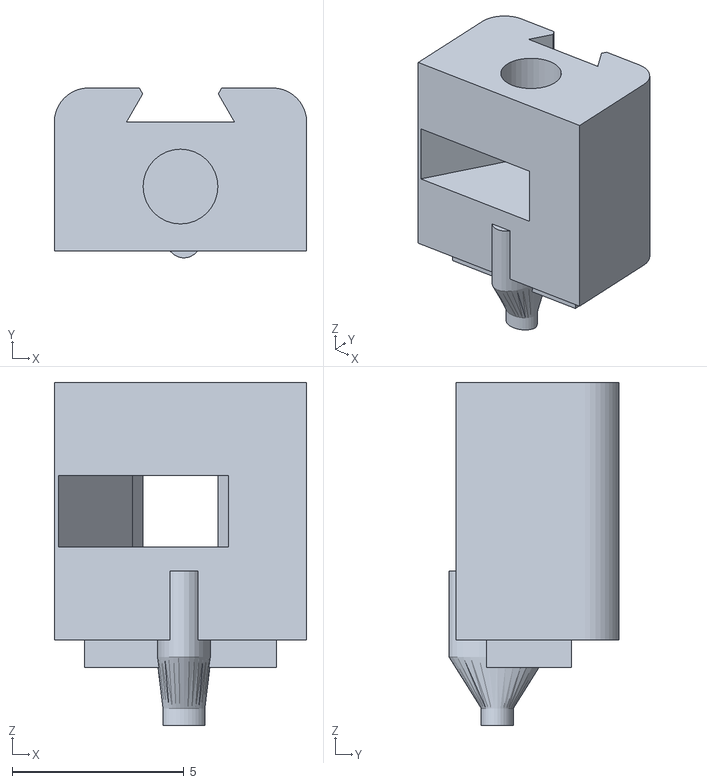
[picture p63: CAD file, 2022-09-09]
blender/stlexports/2022-08-19_12-06-45/stopper0.08.stl
7.36 x 4.96 x 10.0
