esutlie/blender_creations/blender/stlexports/2022-08-19_12-06-52/cover0.1.stl

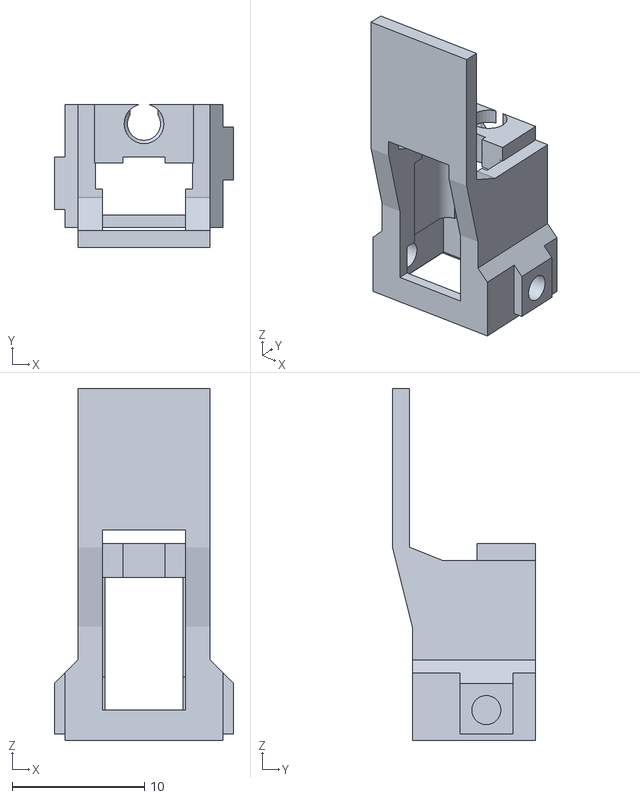
[picture p64: CAD file, 2022-09-09]
blender/stlexports/2022-08-19_12-06-52/cover0.1.stl
13.6 x 10.8 x 26.6
