esutlie/blender_creations/blender/stlexports/2022-08-22_11-59-47/surgery-0.03.stl

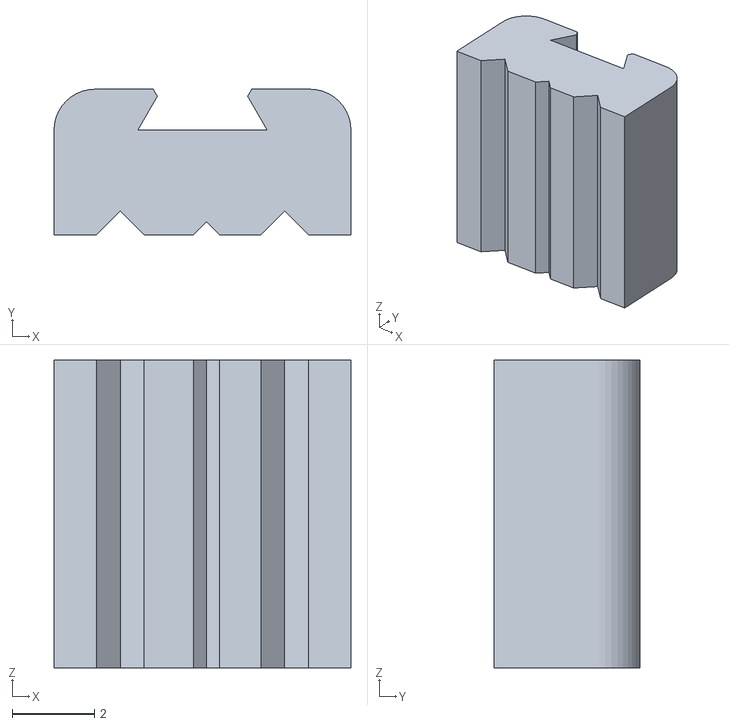
[picture p65: CAD file, 2022-09-09]
blender/stlexports/2022-08-22_11-59-47/surgery-0.03.stl
7.24 x 3.55 x 7.50
