esutlie/blender_creations/blender/stlexports/2022-08-22_11-59-50/stopper0.stl

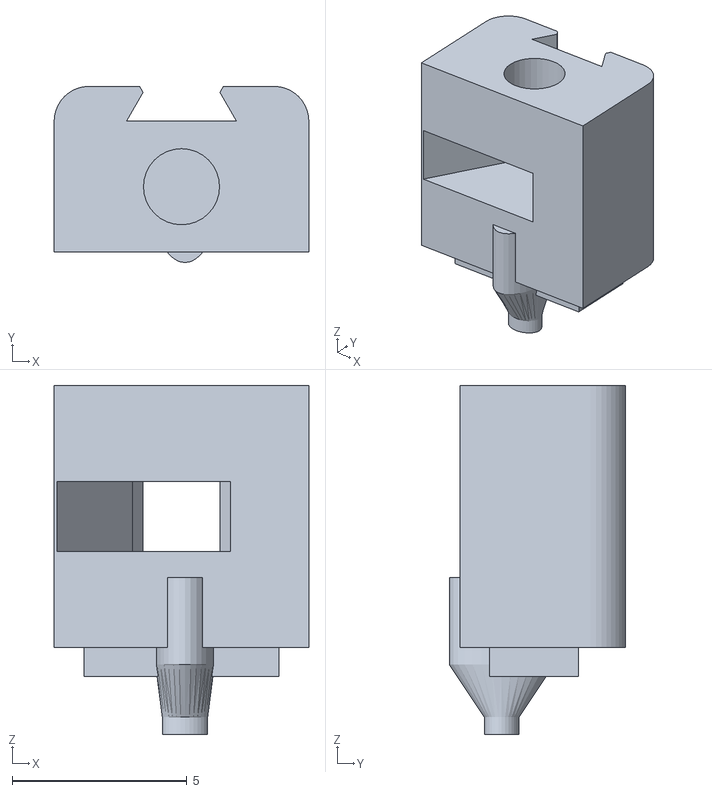
[picture p66: CAD file, 2022-09-09]
blender/stlexports/2022-08-22_11-59-50/stopper0.stl
7.30 x 5.05 x 10.0
