esutlie/blender_creations/blender/stlexports/2022-08-22_11-59-57/surgery0.06.stl

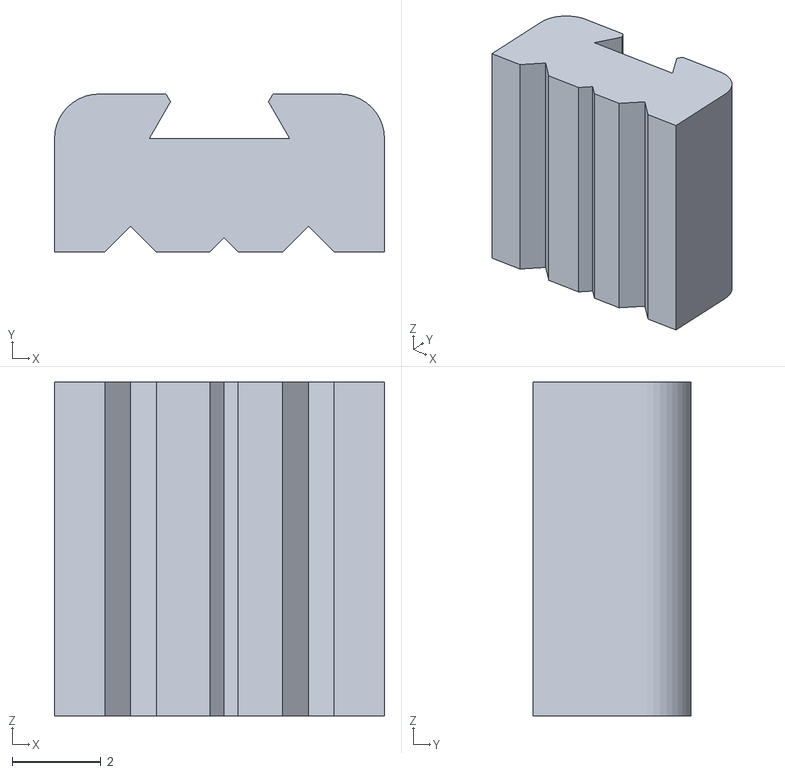
[picture p67: CAD file, 2022-09-09]
blender/stlexports/2022-08-22_11-59-57/surgery0.06.stl
7.42 x 3.55 x 7.50
