esutlie/blender_creations/blender/stlexports/2022-08-22_17-14-55/cover0.02.stl

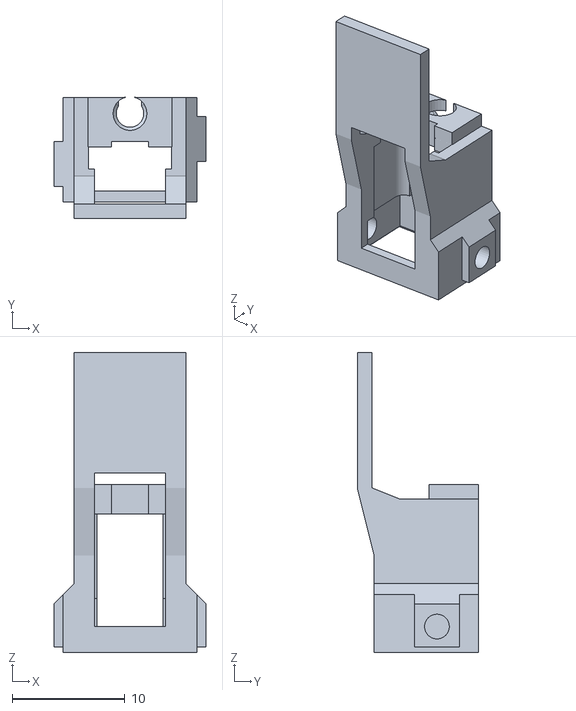
[picture p68: CAD file, 2022-09-09]
blender/stlexports/2022-08-22_17-14-55/cover0.02.stl
13.5 x 10.8 x 26.6
