esutlie/blender_creations/blender/stlexports/2022-08-23_11-19-07/cleaner.stl

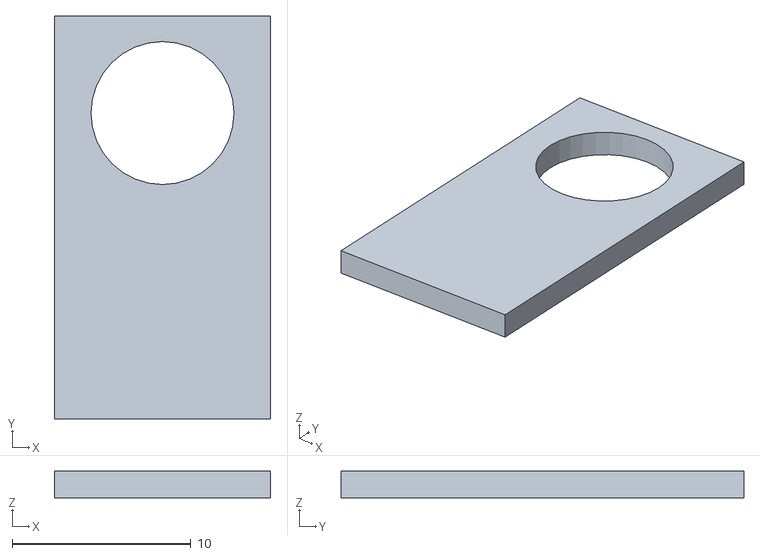
[picture p69: CAD file, 2022-09-09]
blender/stlexports/2022-08-23_11-19-07/cleaner.stl
12.1 x 22.5 x 1.50
