esutlie/blender_creations/blender/stlexports/2022-08-30_17-17-06/holder0.5.stl

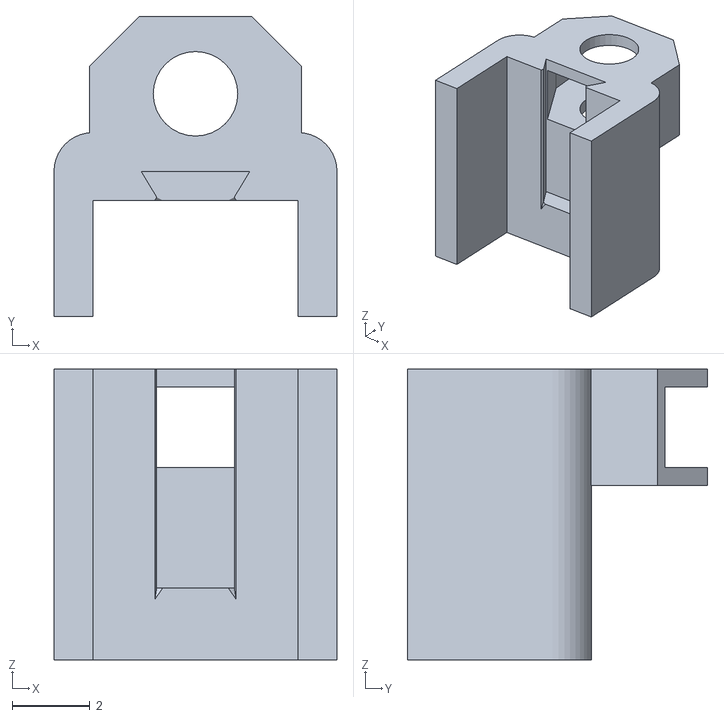
[picture p70: CAD file, 2022-09-09]
blender/stlexports/2022-08-30_17-17-06/holder0.5.stl
7.30 x 7.75 x 7.50
